xxv/motion_nightlight/housing/diffuser.scad

include <motion_nightlight_housing.scad>;

diffuser(interior_battery);
