xxv/motion_nightlight/housing/diffuser_stand.scad

include <motion_nightlight_housing.scad>;

diffuser_stand_print(interior_battery);
