xxv/motion_nightlight/housing/mockup.scad

include <motion_nightlight_housing.scad>;

mockup(interior_battery, diffuser_stand_volume, battery_present=1);
